flakzilla/cr2020-relay-board/CR-2020 reference information/board diagrams/main c board cap map.png

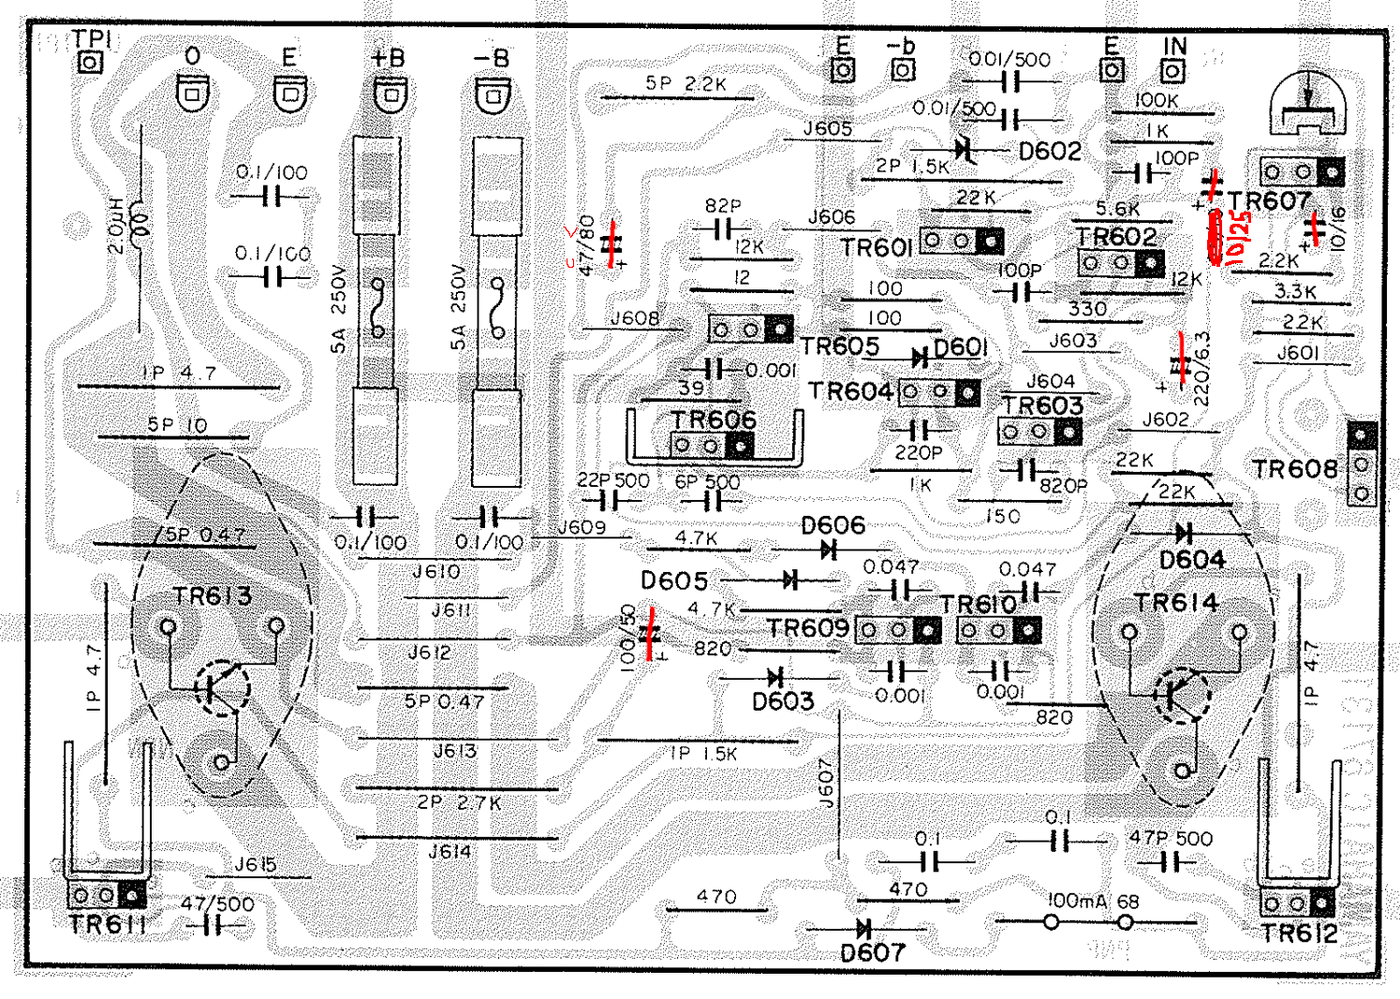
CR-2020 reference information/board diagrams/main c board cap map.png
