flakzilla/cr2020-relay-board/CR-2020 reference information/board diagrams/power supply c board cap map.png

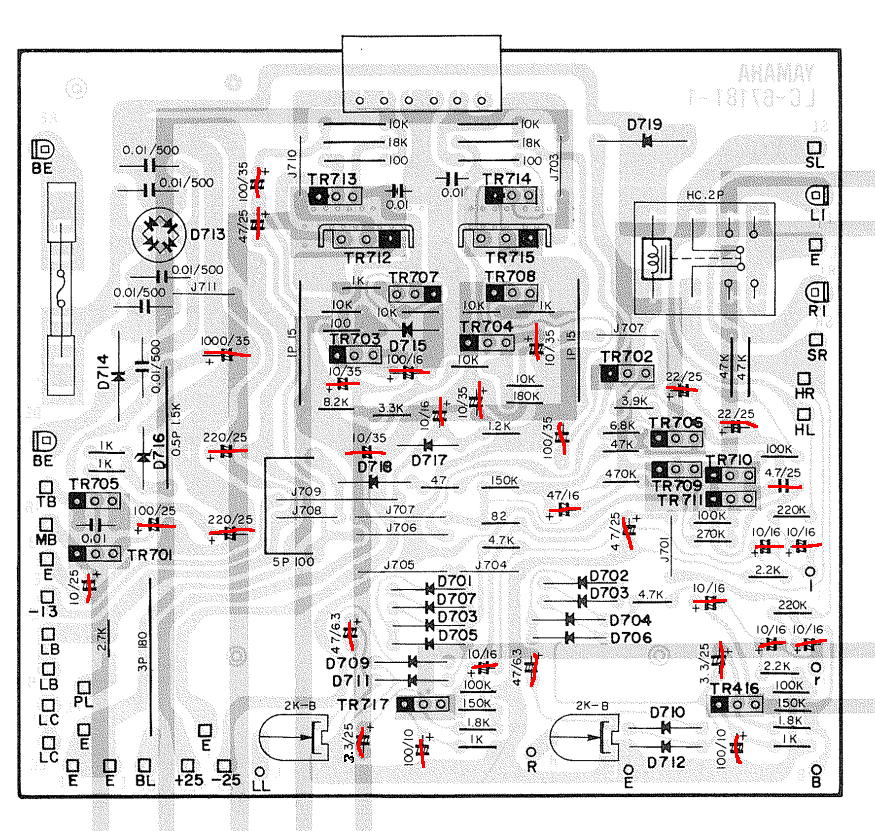
CR-2020 reference information/board diagrams/power supply c board cap map.png
