flakzilla/cr2020-relay-board/CR-2020 reference information/board diagrams/tuner board rear cap map.png

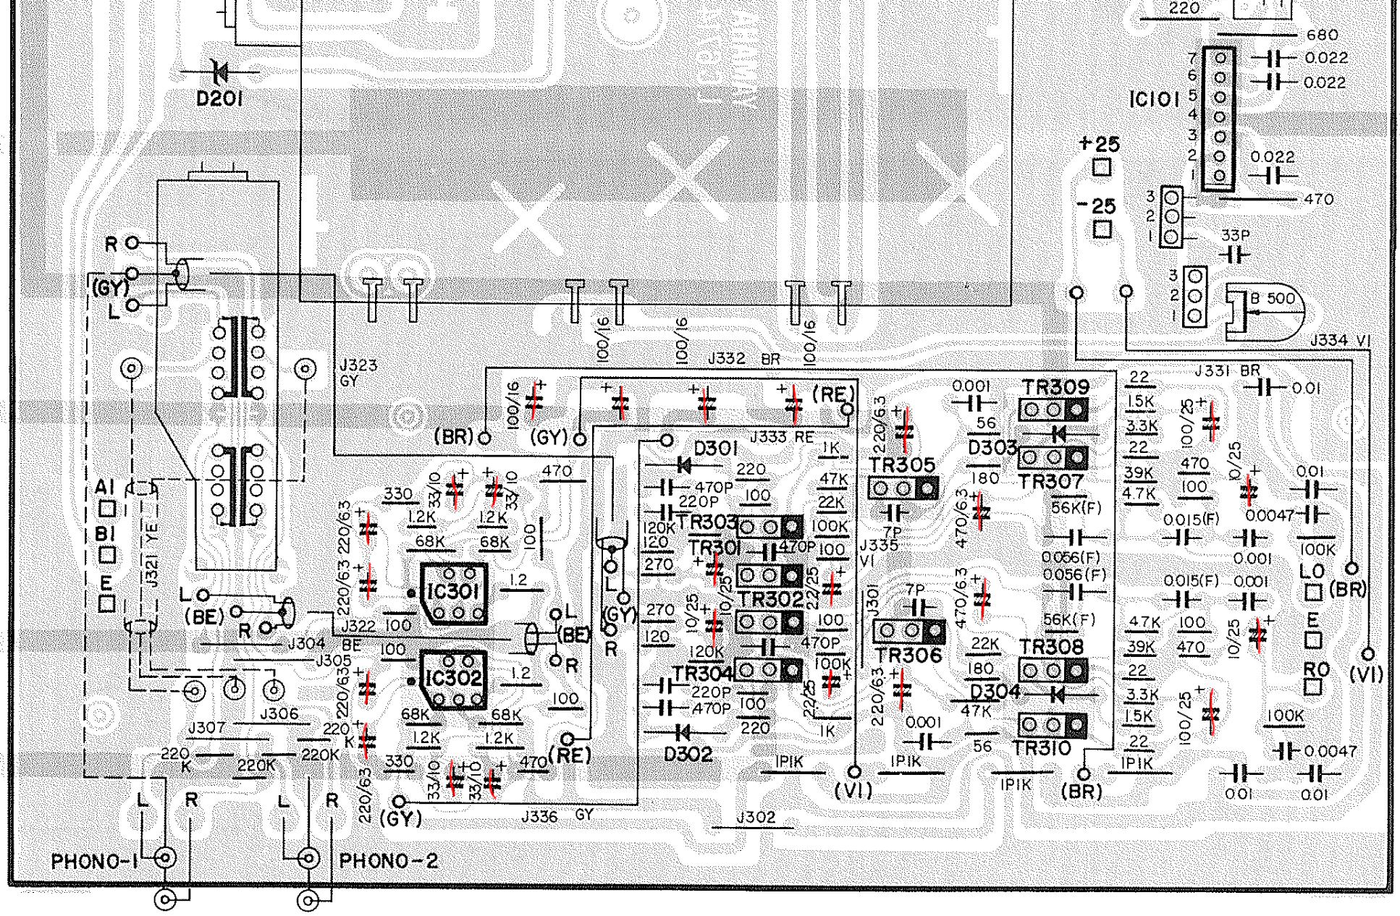
CR-2020 reference information/board diagrams/tuner board rear cap map.png
