flakzilla/cr2020-relay-board/CR-2020 reference information/misc/adimbulbtester.jpg

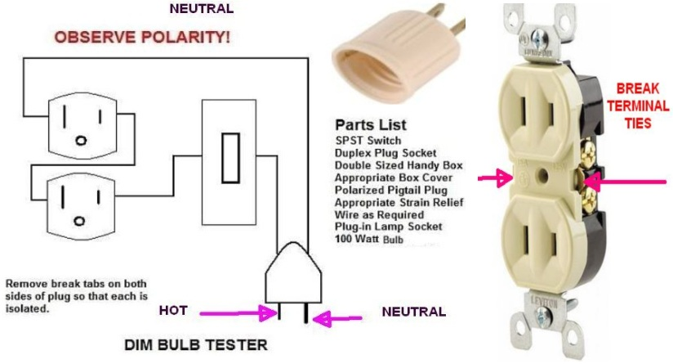
CR-2020 reference information/misc/adimbulbtester.jpg
