flakzilla/cr2020-relay-board/CR-2020 reference information/misc/TR712-715 offboard with fan connector.jpg

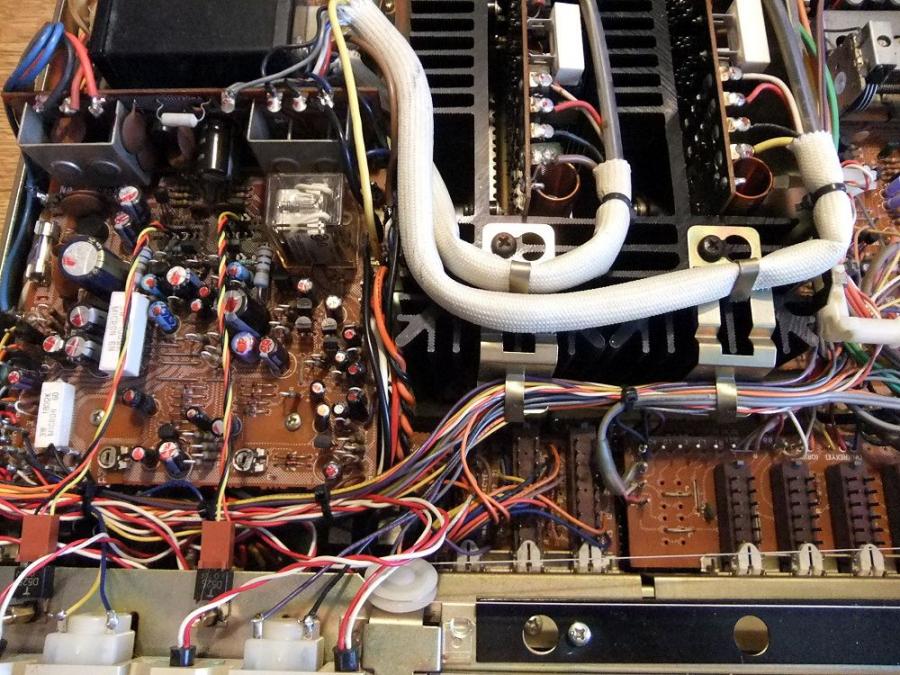
CR-2020 reference information/misc/TR712-715 offboard with fan connector.jpg
