flakzilla/cr2020-relay-board/CR-2020 reference information/service bulletins/2SC458-page-01_2.JPG

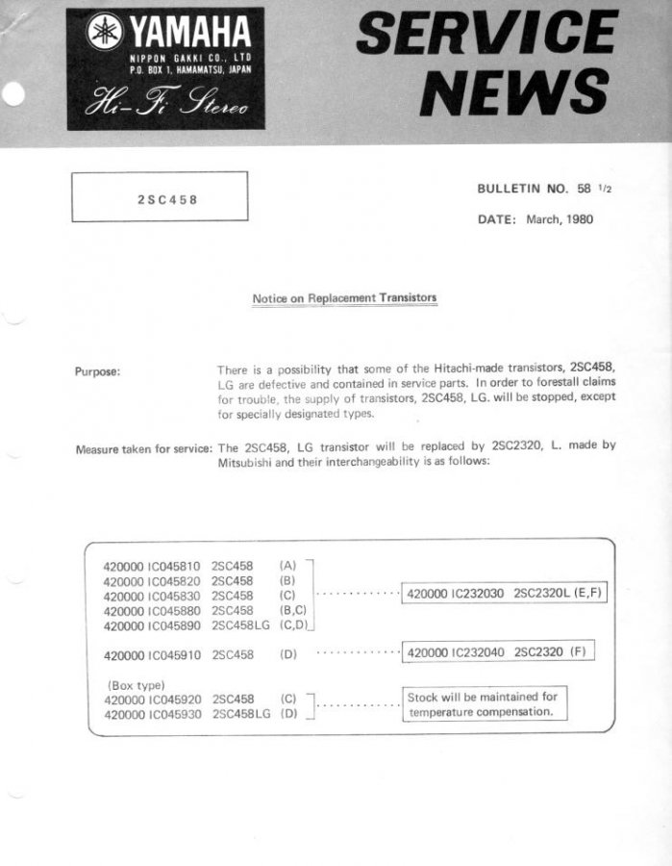
CR-2020 reference information/service bulletins/2SC458-page-01_2.JPG
