flakzilla/cr2020-relay-board/CR-2020 reference information/Yamaha CR-2020 Block Diagram.png

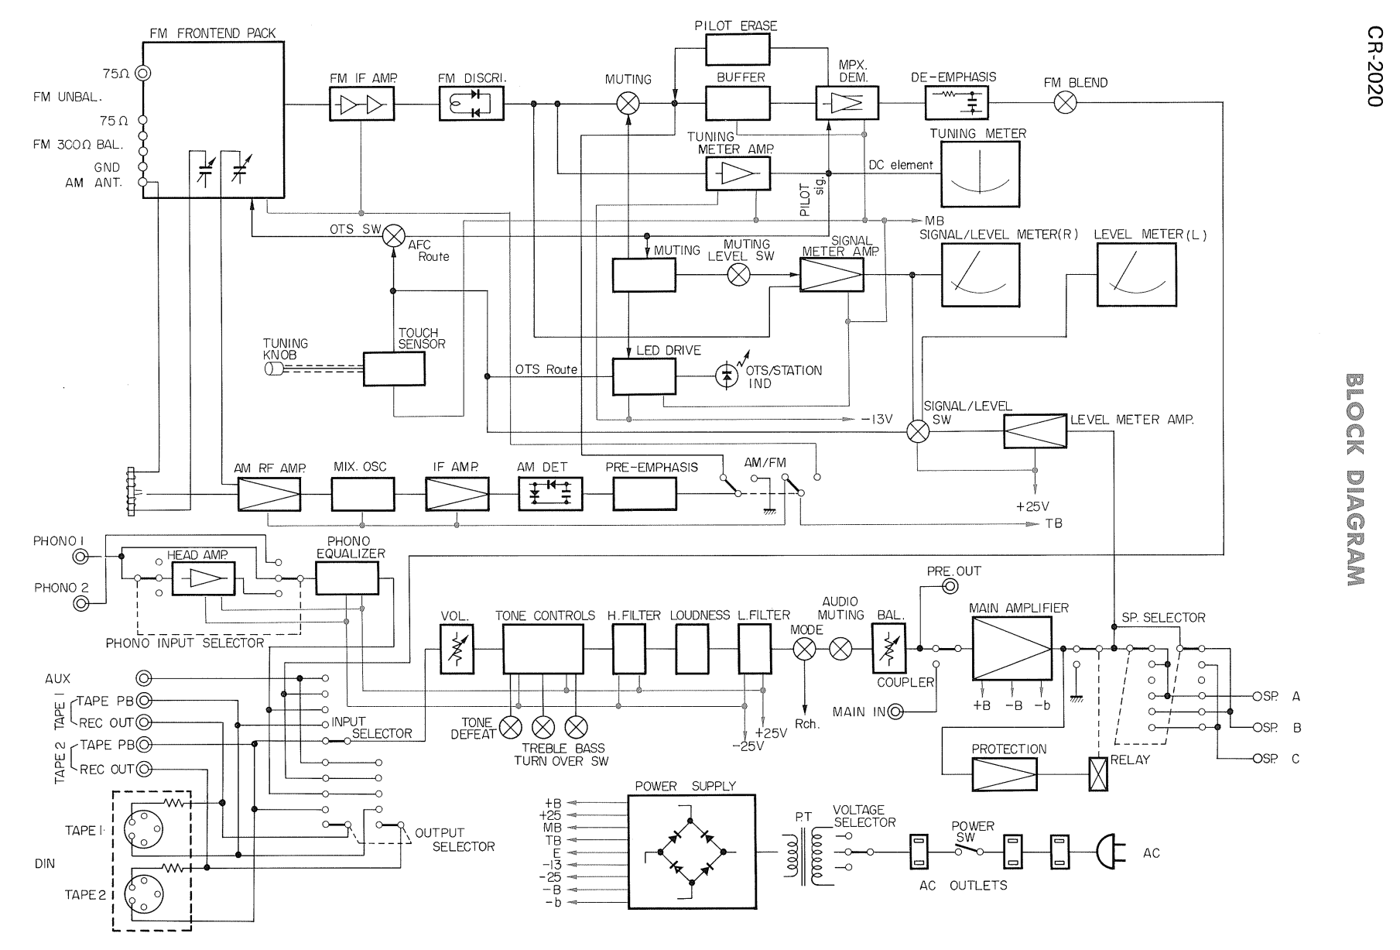
CR-2020 reference information/Yamaha CR-2020 Block Diagram.png
