flakzilla/cr2020-relay-board/CR-2020 relay board LC-67183-1/reference/TO-220 heatsink/Option 1/IMG_6089.JPG

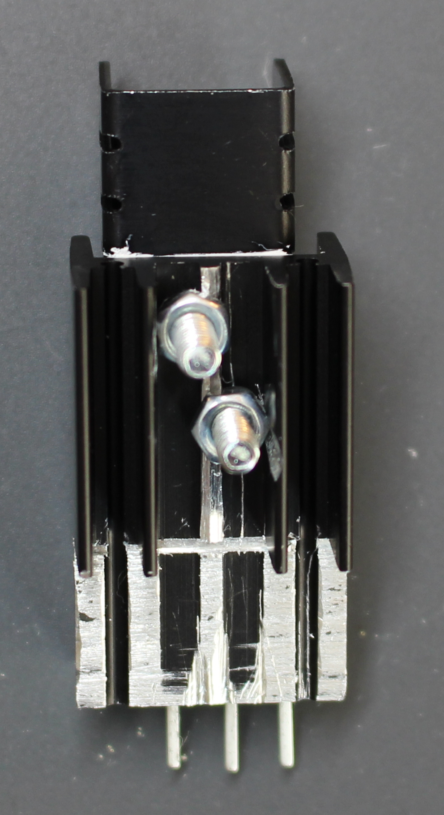
CR-2020 relay board LC-67183-1/reference/TO-220 heatsink/Option 1/IMG_6089.JPG
