flakzilla/cr2020-relay-board/CR-2020 relay board LC-67183-1/reference/TO-220 heatsink/Option 2/IMG_6072.JPG

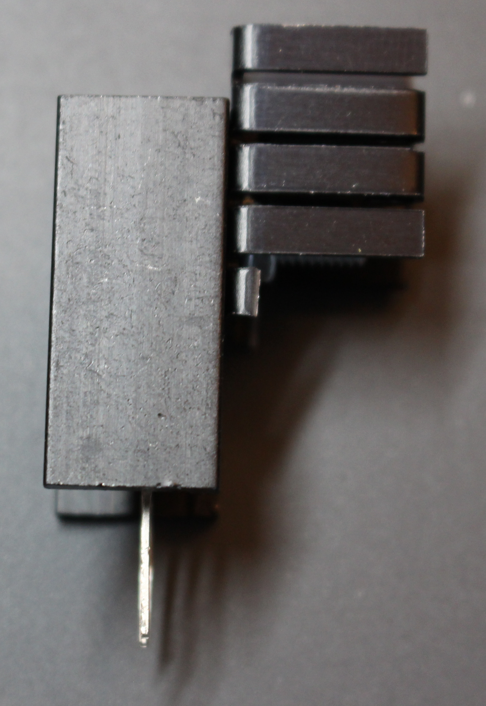
CR-2020 relay board LC-67183-1/reference/TO-220 heatsink/Option 2/IMG_6072.JPG
