flakzilla/cr2020-relay-board/CR-2020 reference information/board diagrams/electrolytic cap c board parts list.png

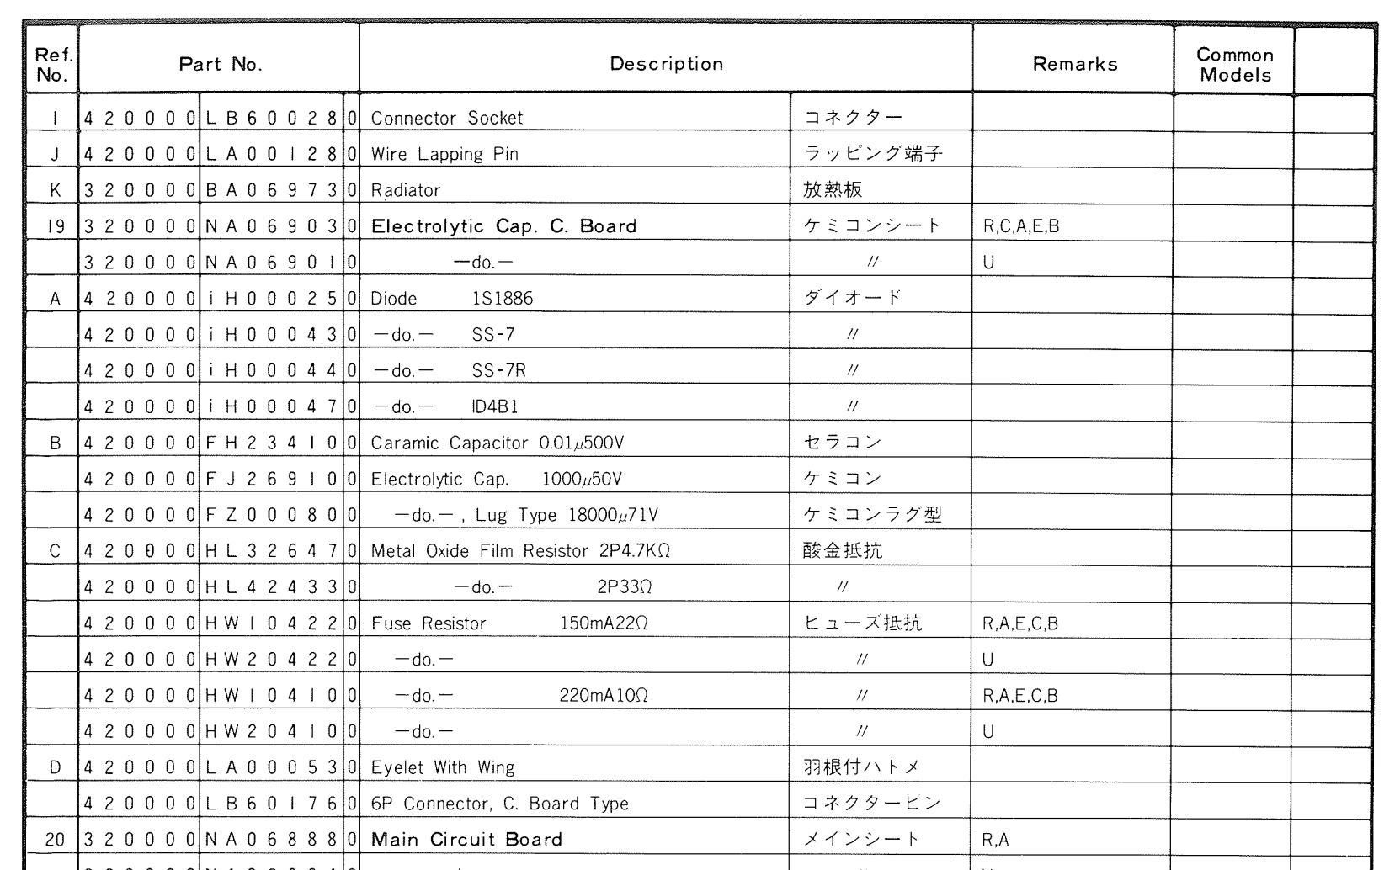
CR-2020 reference information/board diagrams/electrolytic cap c board parts list.png
